RBSC/FLEX/Engraving/flex_rbsc.bmp

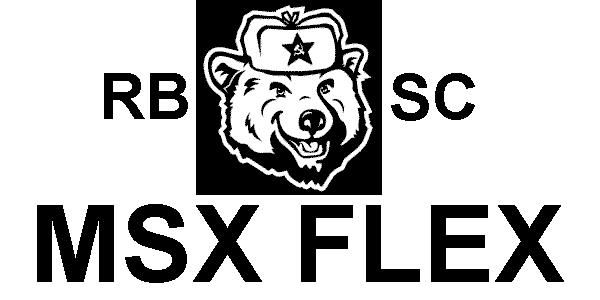
Engraving/flex_rbsc.bmp
