RBSC/FLEX/Pics/ready.jpg

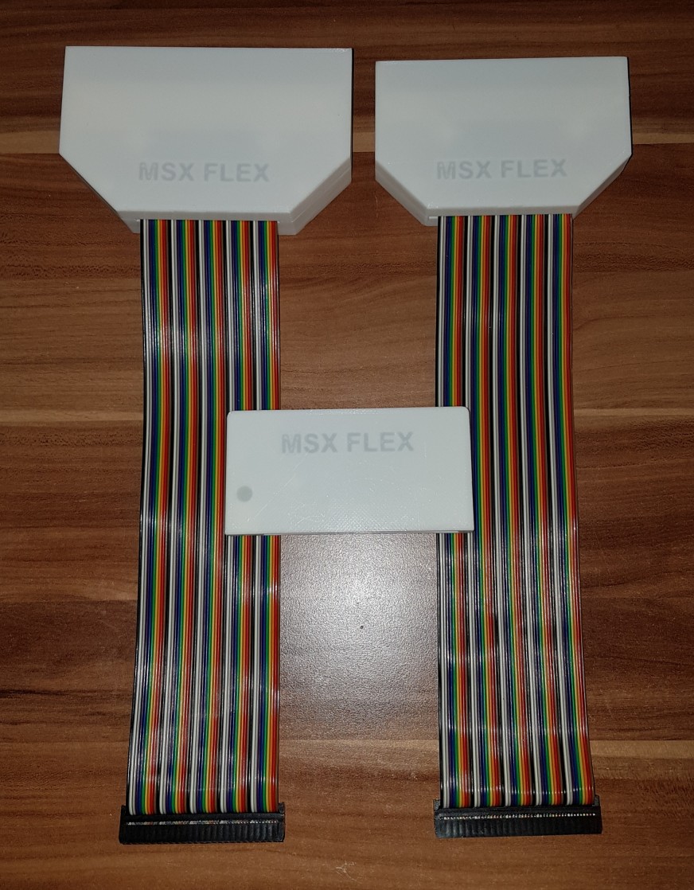
Pics/ready.jpg
