RBSC/FLEX/Pics/slot_converter.jpg

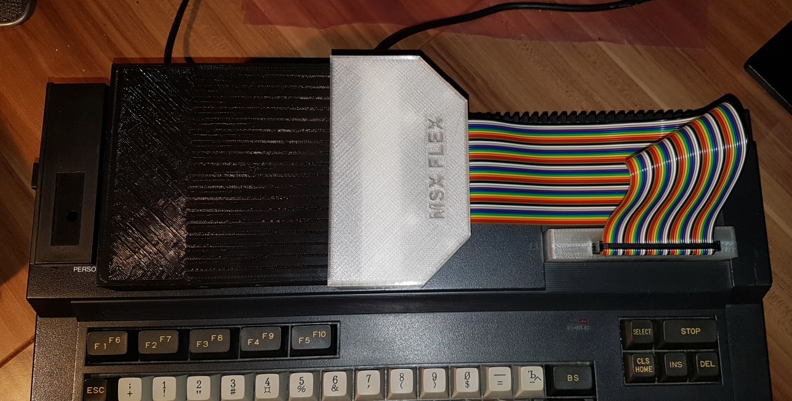
Pics/slot_converter.jpg
